ProyectoDatos2/Datos2/Imagenes/PCB/Pines MOSFET 1.jpg

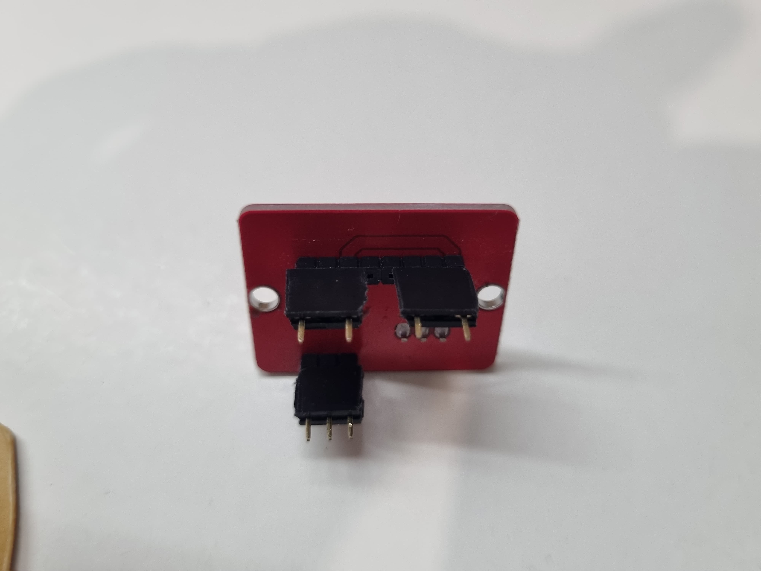
Imagenes/PCB/Pines MOSFET 1.jpg
