ProyectoDatos2/Datos2/Imagenes/PCB/Pines MOSFET 2.jpg

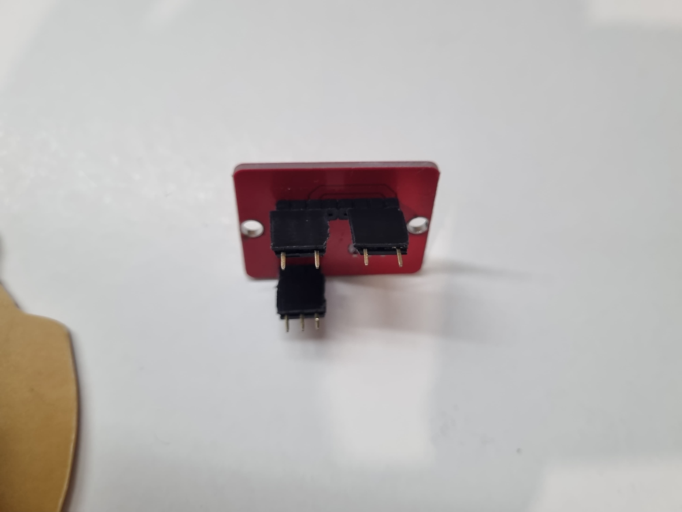
Imagenes/PCB/Pines MOSFET 2.jpg
