ProyectoDatos2/Datos2/Imagenes/PCB/Pines Placa.png

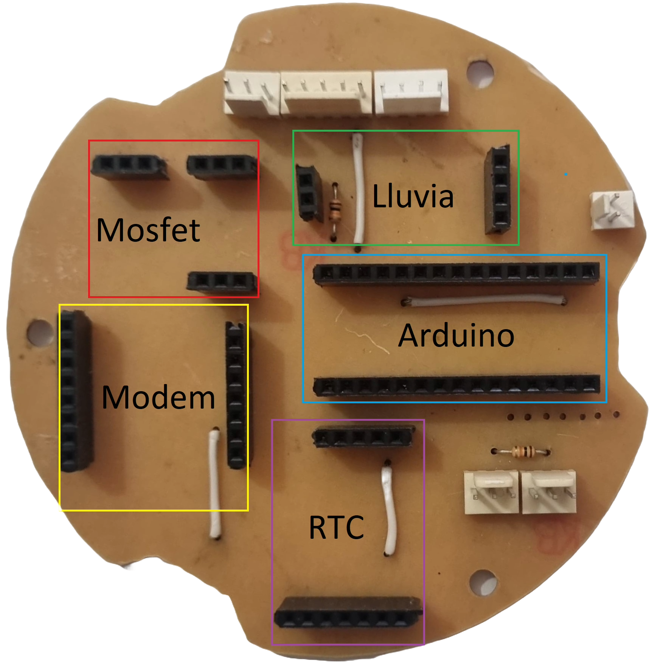
Imagenes/PCB/Pines Placa.png
