ProyectoDatos2/Datos2/Imagenes/PCB/Placa Terminada.png

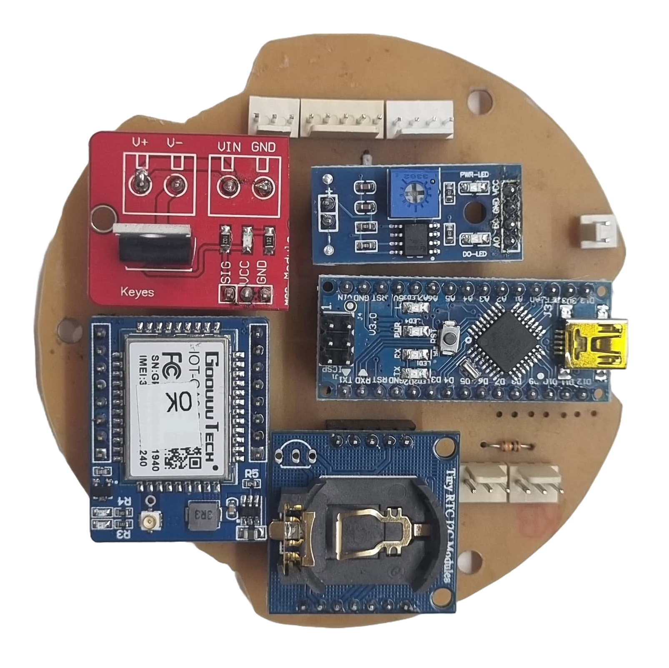
Imagenes/PCB/Placa Terminada.png
