ProyectoDatos2/Datos2/Imagenes/PCB/Posicion Pila RTC.jpg

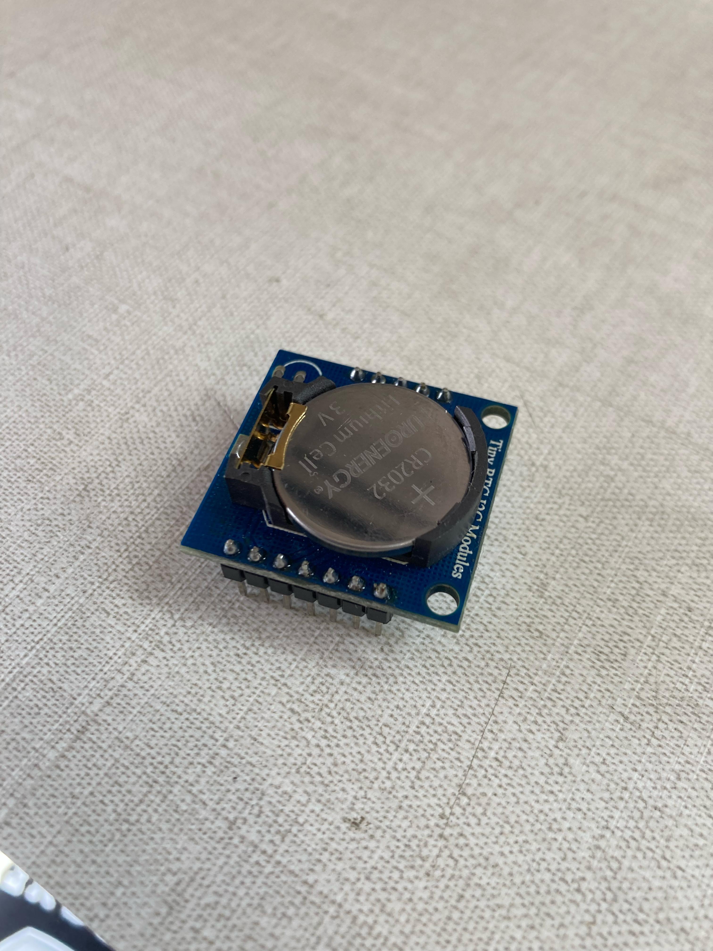
Imagenes/PCB/Posicion Pila RTC.jpg
