ProyectoDatos2/Datos2/Imagenes/PCB/Prensa Cables para Antena.jpg

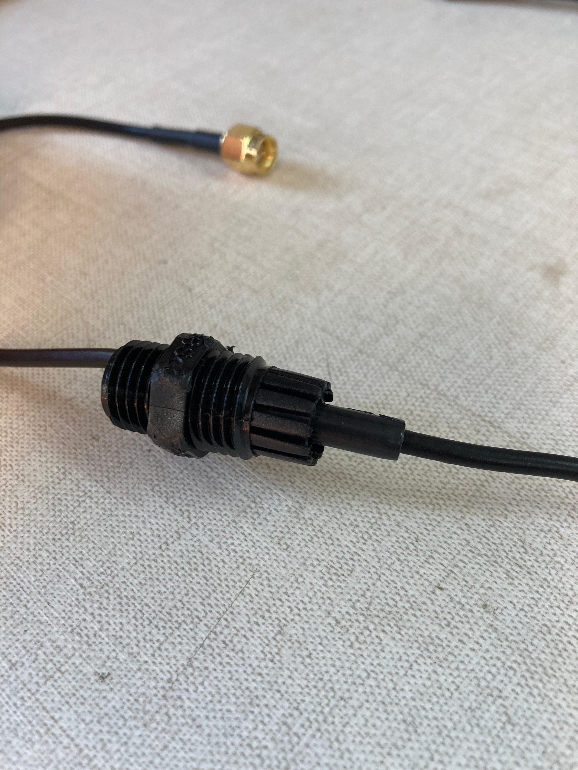
Imagenes/PCB/Prensa Cables para Antena.jpg
