ProyectoDatos2/Datos2/Imagenes/PCB/Componentes Necesarios.jpg

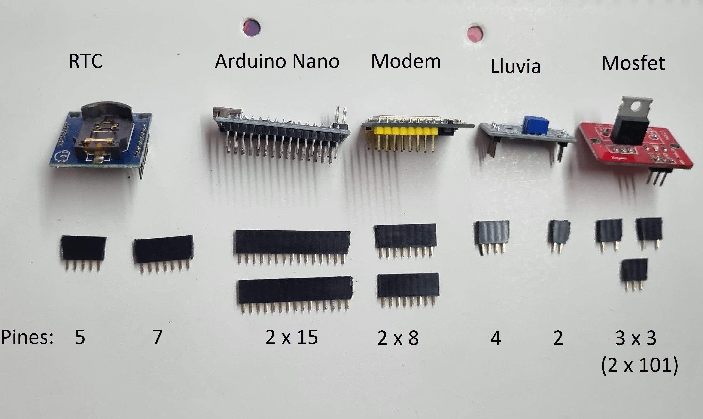
Imagenes/PCB/Componentes Necesarios.jpg
