ProyectoDatos2/Datos2/Impresion 3D STL/Telemetría/Tel_Holder Step Up.STL

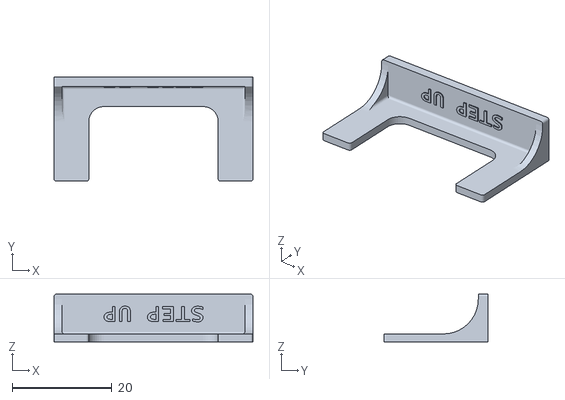
[picture p59: CAD file, 2023-10-26]
Impresion 3D STL/Telemetría/Tel_Holder Step Up.STL
40.0 x 21.0 x 9.60
