ProyectoDatos2/Datos2/Impresion 3D STL/Pluviómetro/Pluv_Estanco A.STL

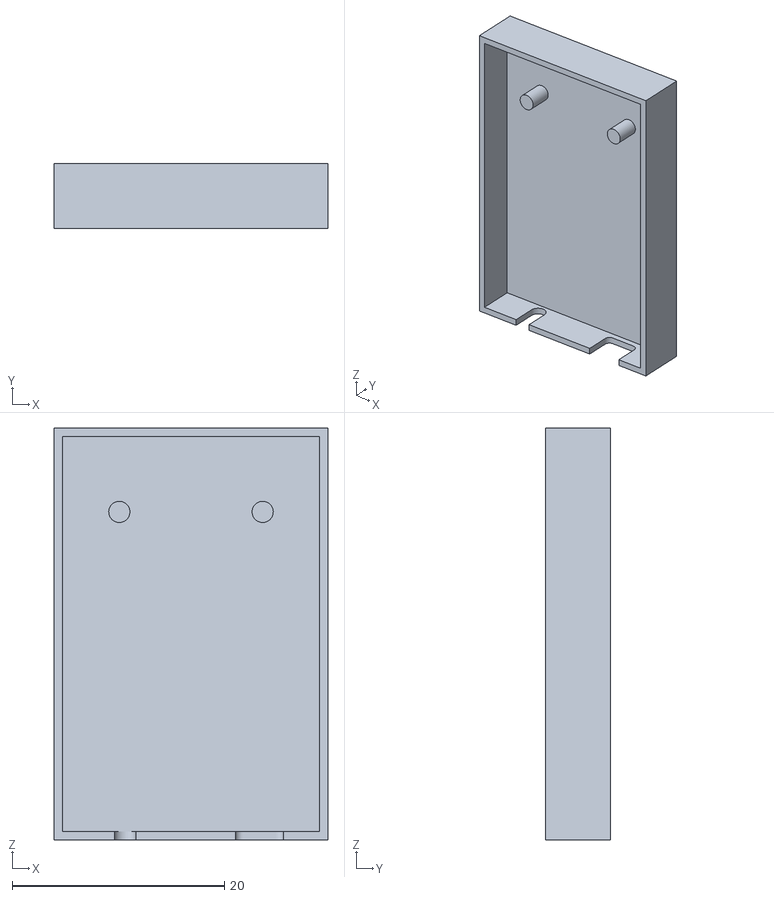
[picture p60: CAD file, 2023-10-26]
Impresion 3D STL/Pluviómetro/Pluv_Estanco A.STL
25.8 x 6.10 x 38.8
