ProyectoDatos2/Datos2/Impresion 3D STL/Telemetría/Tel_Tope.STL

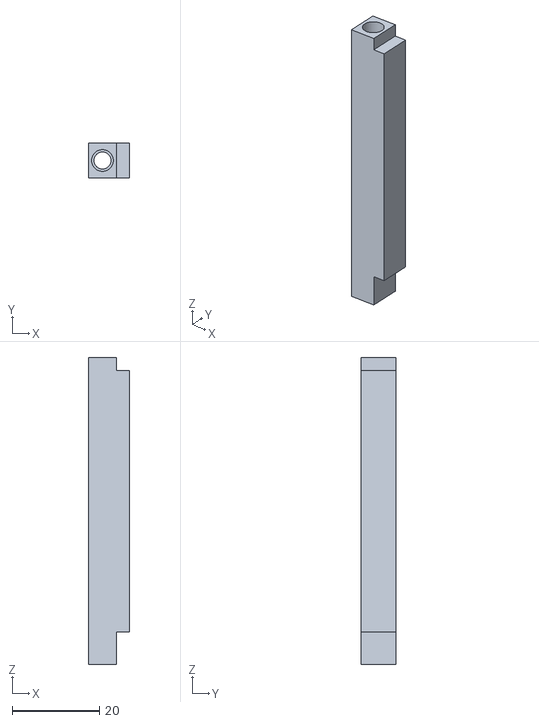
[picture p61: CAD file, 2023-10-26]
Impresion 3D STL/Telemetría/Tel_Tope.STL
9.50 x 8.00 x 70.5
