ProyectoDatos2/Datos2/Impresion 3D STL/Pluviómetro/Pluv_Aro.STL

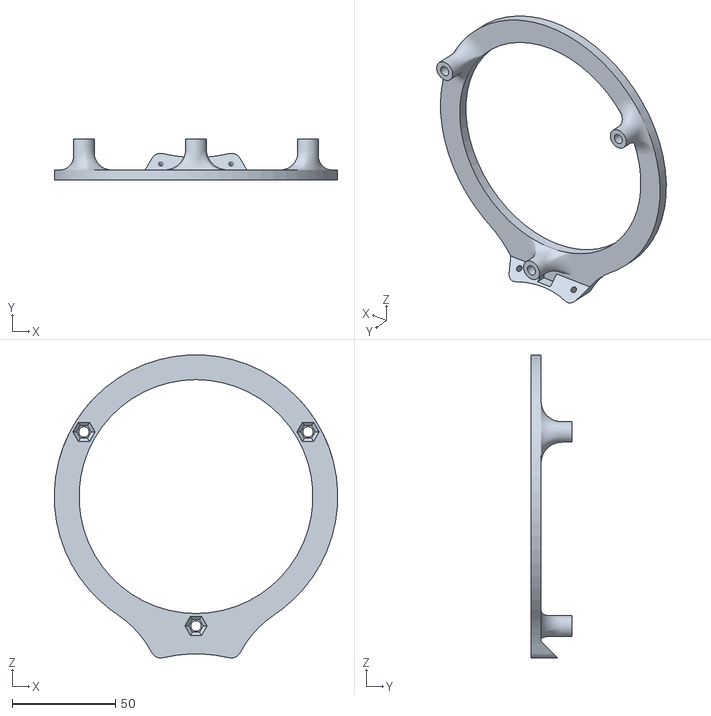
[picture p62: CAD file, 2023-10-26]
Impresion 3D STL/Pluviómetro/Pluv_Aro.STL
136.9 x 20.0 x 146.4
