ProyectoDatos2/Datos2/Impresion 3D STL/Telemetría/Tel_Tapa Inferior.STL

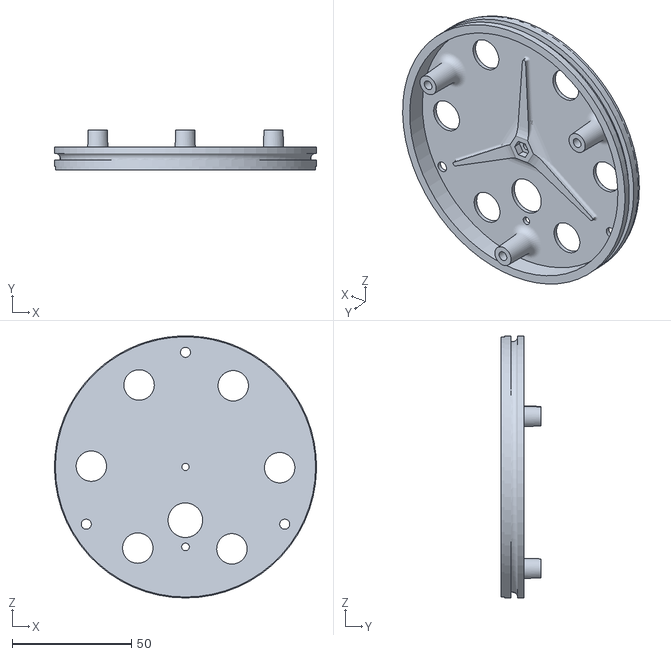
[picture p63: CAD file, 2023-10-26]
Impresion 3D STL/Telemetría/Tel_Tapa Inferior.STL
109.8 x 16.6 x 109.7
