ProyectoDatos2/Datos2/Impresion 3D STL/Pluviómetro/Pluv_Tapa.STL

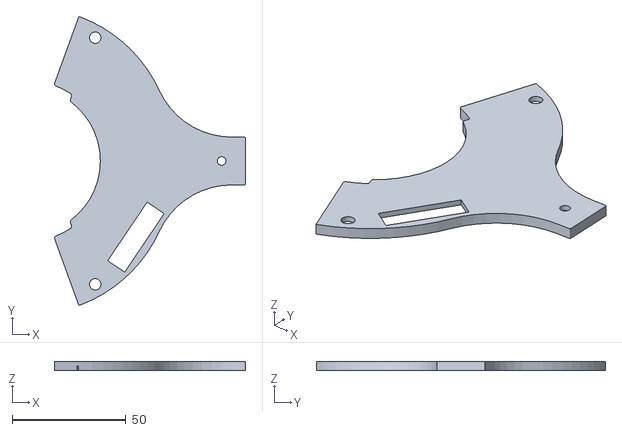
[picture p64: CAD file, 2023-10-26]
Impresion 3D STL/Pluviómetro/Pluv_Tapa.STL
83.8 x 126.9 x 4.00
