ProyectoDatos2/Datos2/Impresion 3D STL/Telemetría/Tel_Pieza T.STL

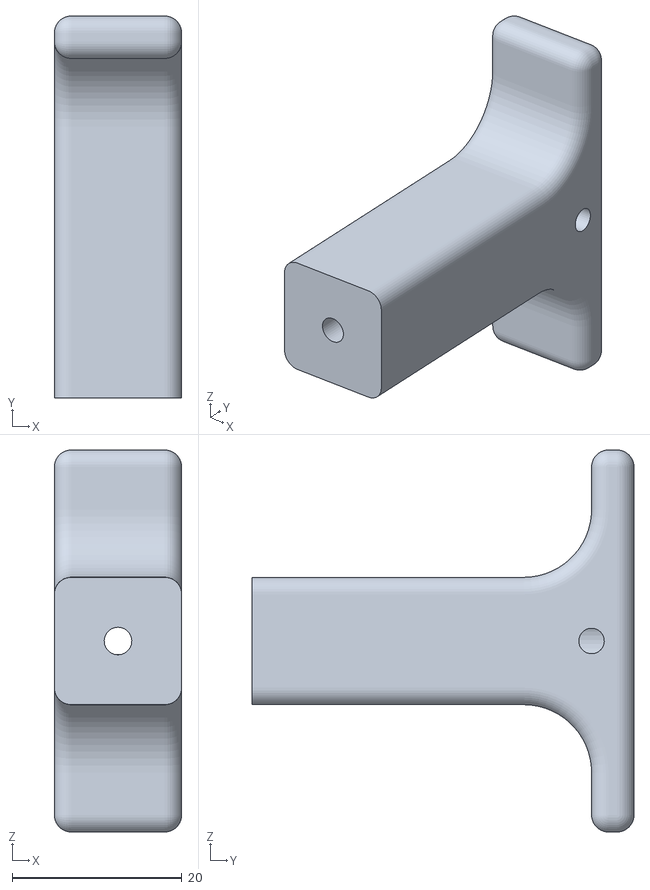
[picture p65: CAD file, 2023-10-26]
Impresion 3D STL/Telemetría/Tel_Pieza T.STL
15.0 x 45.0 x 45.0
