ProyectoDatos2/Datos2/Impresion 3D STL/Telemetría/Tel_Separador.STL

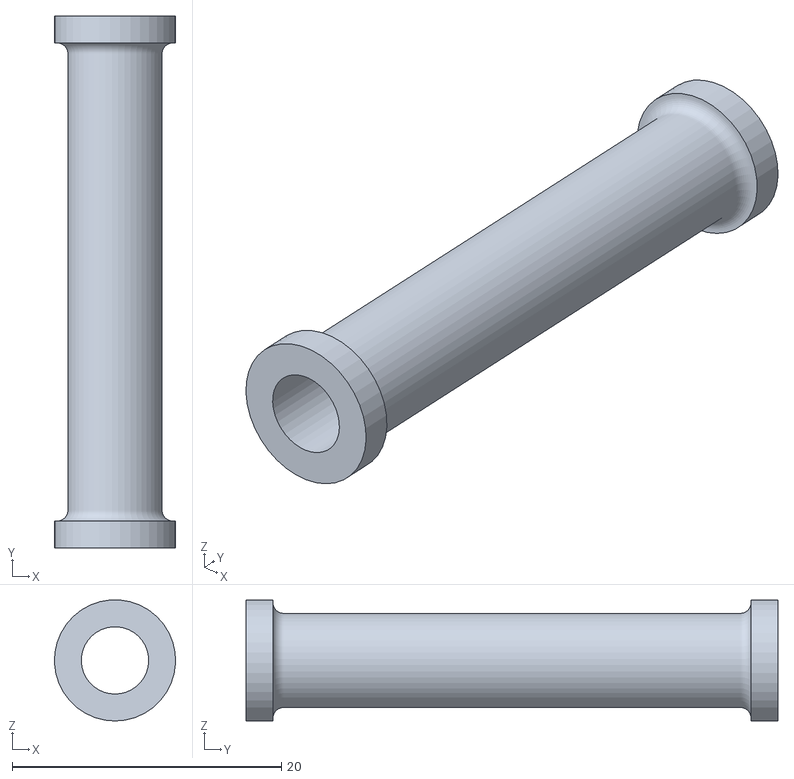
[picture p66: CAD file, 2023-10-26]
Impresion 3D STL/Telemetría/Tel_Separador.STL
8.99 x 39.5 x 8.98
