ProyectoDatos2/Datos2/Imagenes/Ensamble/Conjunto Pluviómetro/Arandelas Localizador.jpg

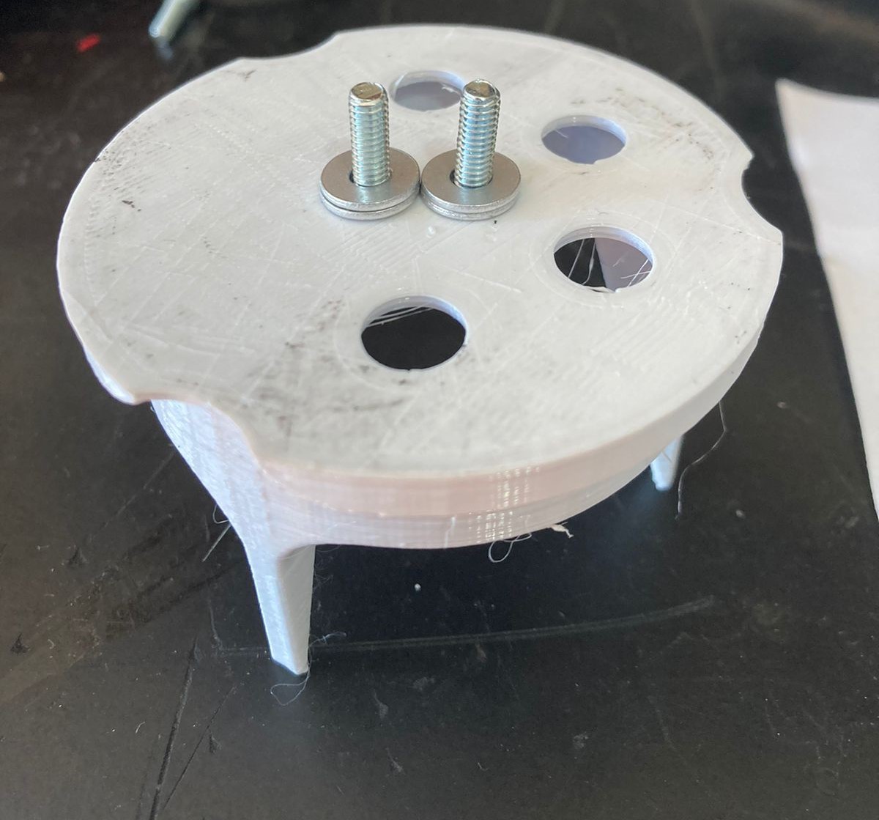
Imagenes/Ensamble/Conjunto Pluviómetro/Arandelas Localizador.jpg
