ProyectoDatos2/Datos2/Imagenes/Ensamble/Conjunto Pluviómetro/Colocacion Driver Celda de Carga 2.jpg

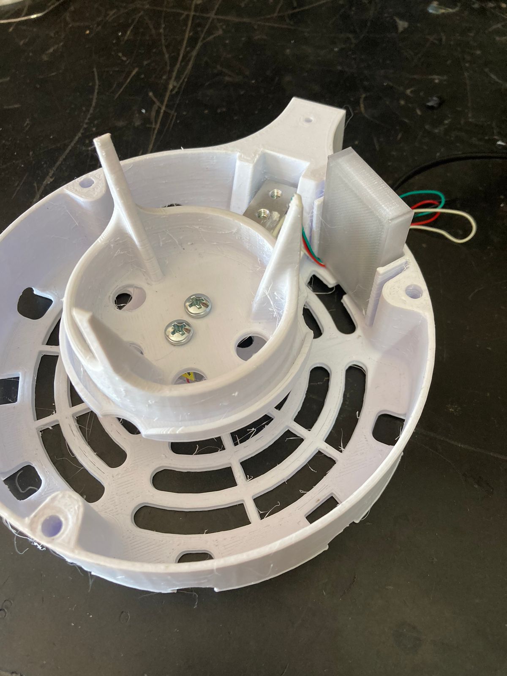
Imagenes/Ensamble/Conjunto Pluviómetro/Colocacion Driver Celda de Carga 2.jpg
