ProyectoDatos2/Datos2/Imagenes/Ensamble/Conjunto Pluviómetro/Colocación Mensula.jpg

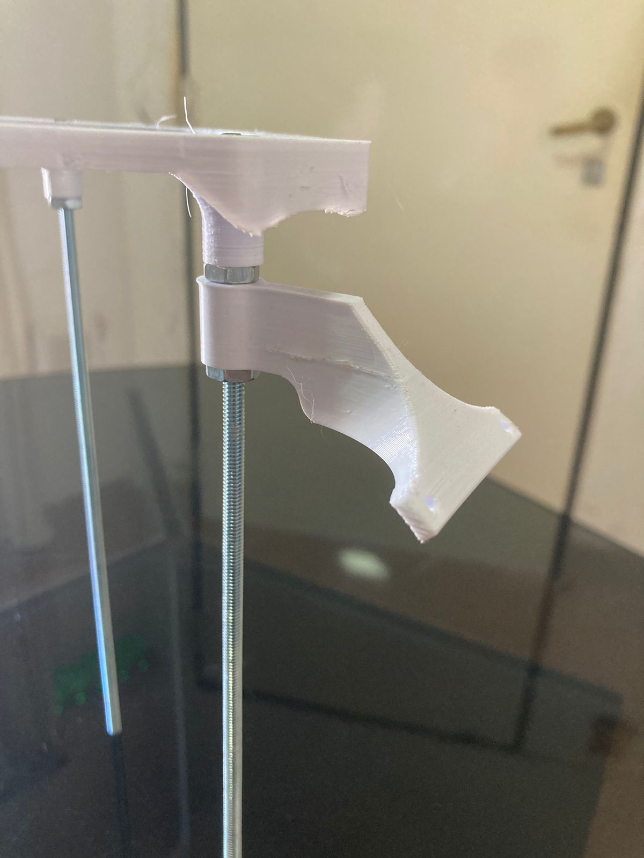
Imagenes/Ensamble/Conjunto Pluviómetro/Colocación Mensula.jpg
