ProyectoDatos2/Datos2/Imagenes/Ensamble/Conjunto Pluviómetro/Colocación Tapa.jpg

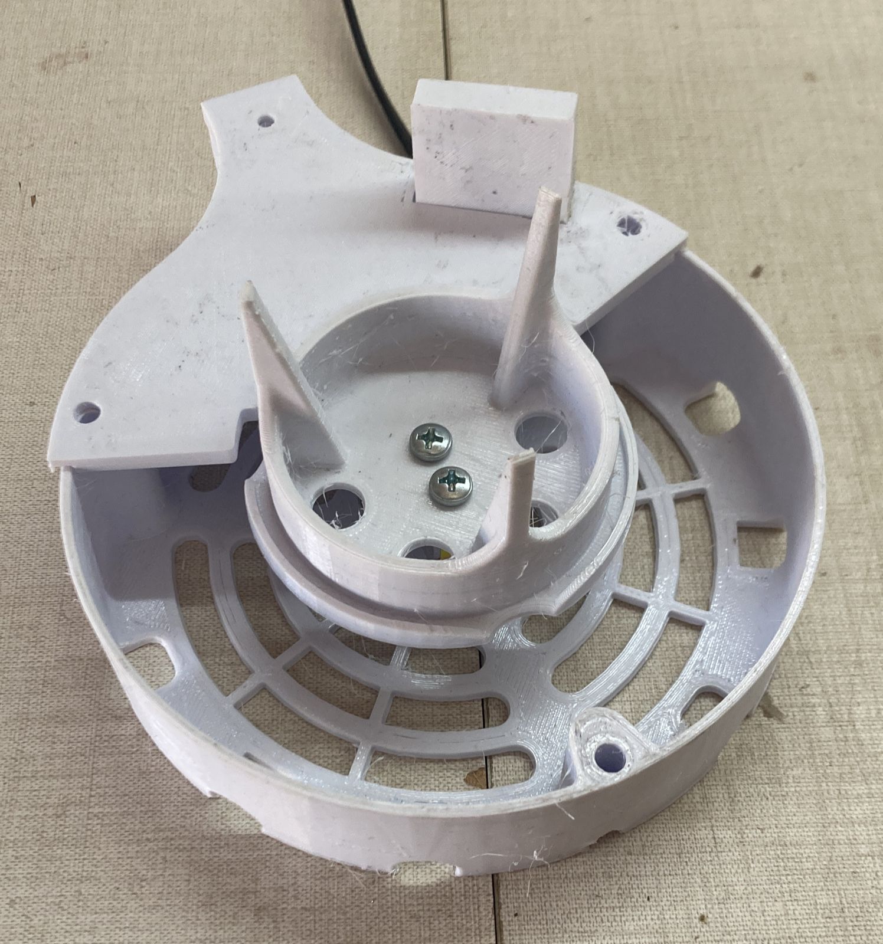
Imagenes/Ensamble/Conjunto Pluviómetro/Colocación Tapa.jpg
