ProyectoDatos2/Datos2/Imagenes/Ensamble/Conjunto Pluviómetro/Conexión Celda de Carga.png

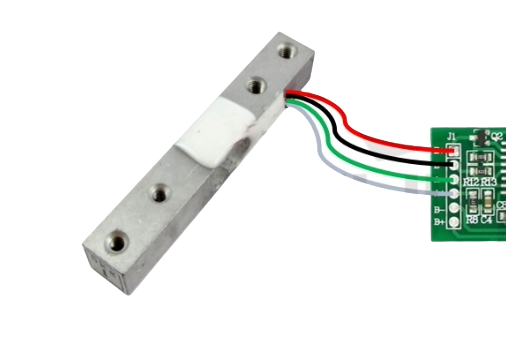
Imagenes/Ensamble/Conjunto Pluviómetro/Conexión Celda de Carga.png
