ProyectoDatos2/Datos2/Imagenes/Ensamble/Conjunto Pluviómetro/Nivel 1.jpg

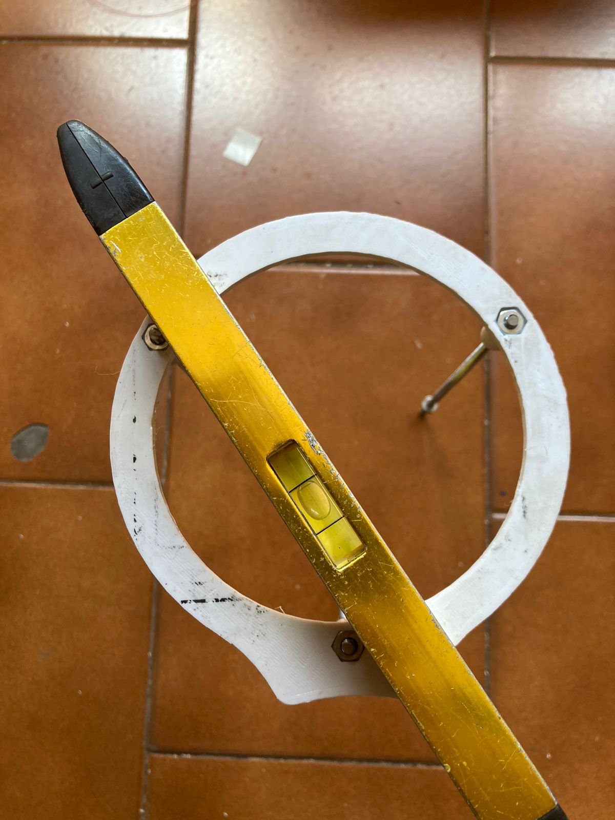
Imagenes/Ensamble/Conjunto Pluviómetro/Nivel 1.jpg
