ProyectoDatos2/Datos2/Imagenes/Ensamble/Conjunto Pluviómetro/Nivel 2.jpg

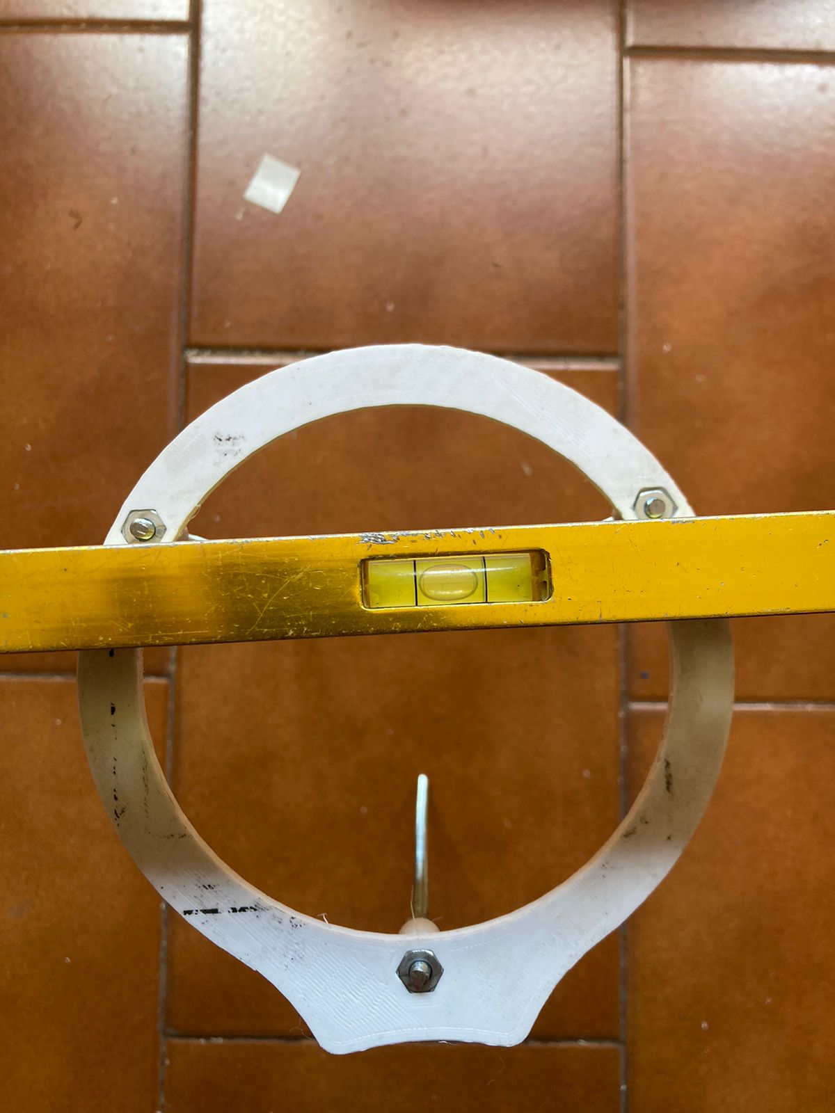
Imagenes/Ensamble/Conjunto Pluviómetro/Nivel 2.jpg
