ProyectoDatos2/Datos2/Imagenes/Ensamble/Conjunto Pluviómetro/Nivel 3.jpg

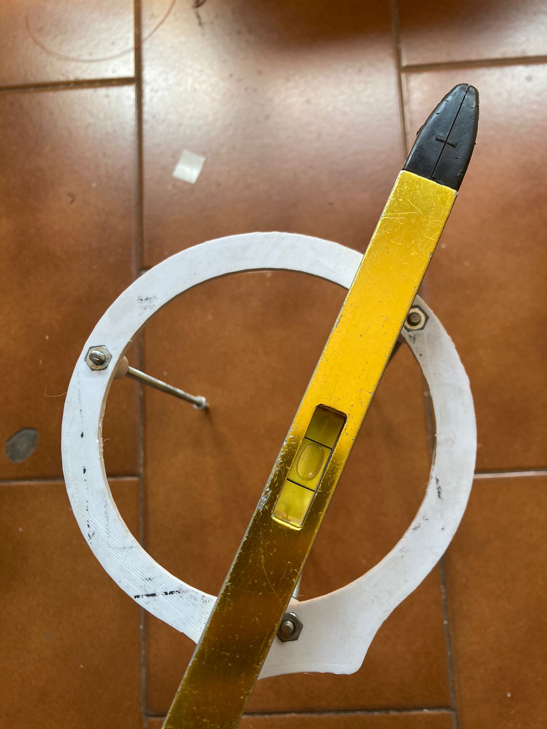
Imagenes/Ensamble/Conjunto Pluviómetro/Nivel 3.jpg
