ProyectoDatos2/Datos2/Imagenes/Ensamble/Conjunto Pluviómetro/Orientacion Localizador.jpg

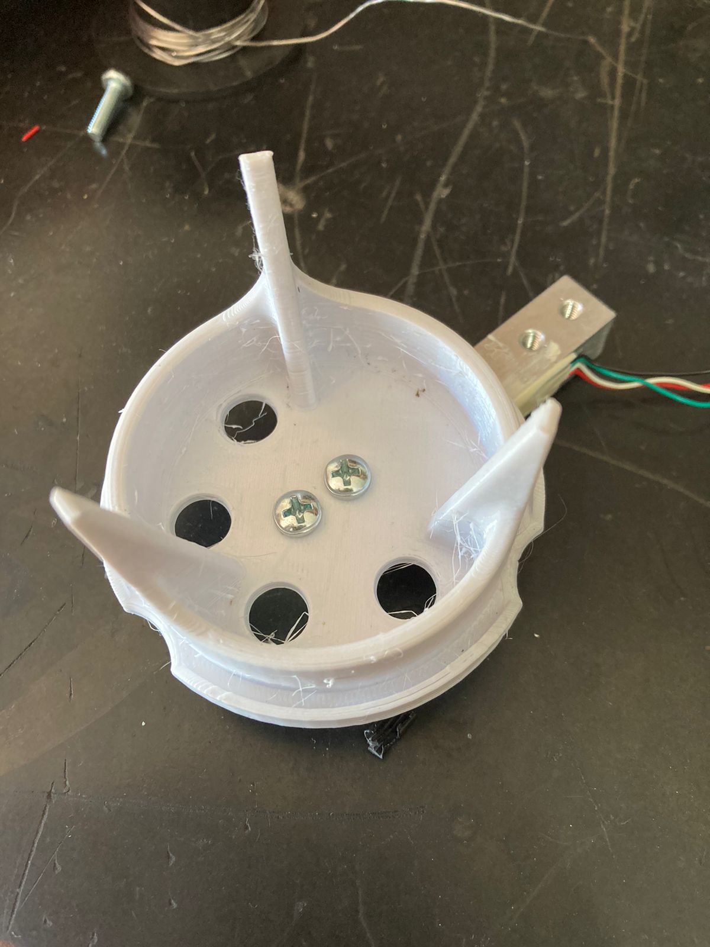
Imagenes/Ensamble/Conjunto Pluviómetro/Orientacion Localizador.jpg
