ProyectoDatos2/Datos2/Imagenes/Ensamble/Conjunto Pluviómetro/Orientación Celda de Carga.jpg

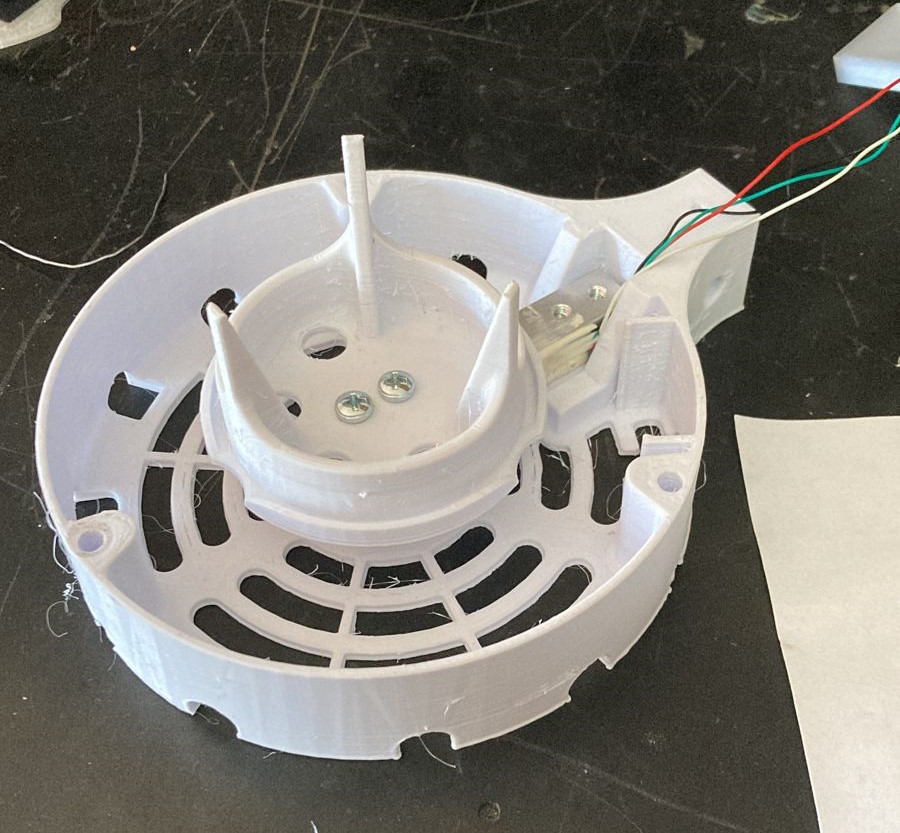
Imagenes/Ensamble/Conjunto Pluviómetro/Orientación Celda de Carga.jpg
