ProyectoDatos2/Datos2/Imagenes/Ensamble/Conjunto Pluviómetro/Pintado y Colocacion Sensor Raindrop.png

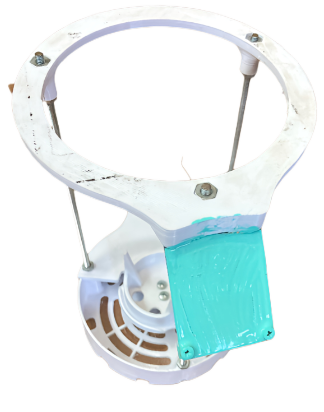
Imagenes/Ensamble/Conjunto Pluviómetro/Pintado y Colocacion Sensor Raindrop.png
