ProyectoDatos2/Datos2/Imagenes/Ensamble/Conjunto Pluviómetro/Roscas por Abajo.jpg

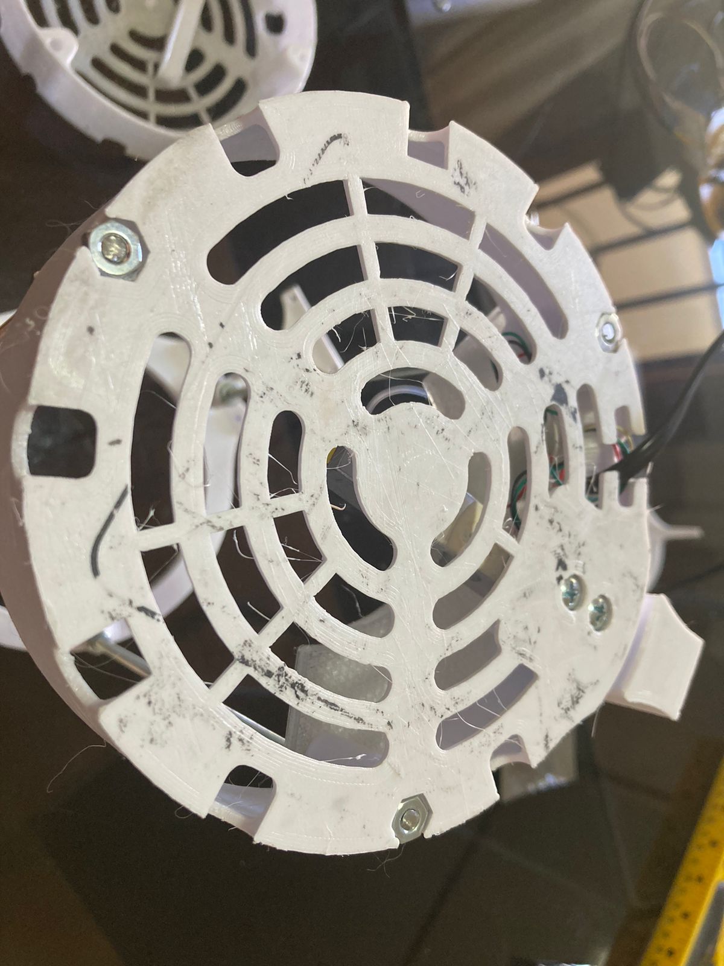
Imagenes/Ensamble/Conjunto Pluviómetro/Roscas por Abajo.jpg
