ProyectoDatos2/Datos2/Imagenes/Ensamble/Conjunto Pluviómetro/Terminado.png

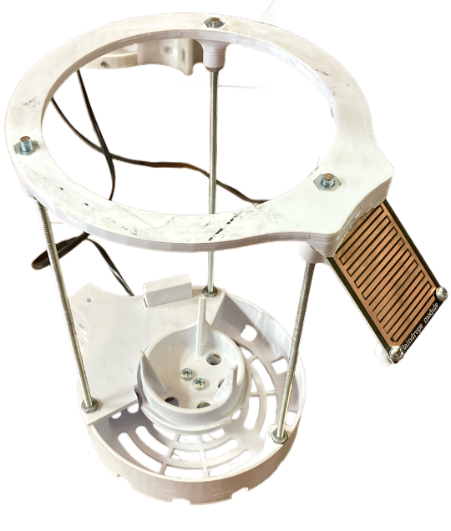
Imagenes/Ensamble/Conjunto Pluviómetro/Terminado.png
