ProyectoDatos2/Datos2/Imagenes/Ensamble/Conjunto UV/Colocación Sensor UV.png

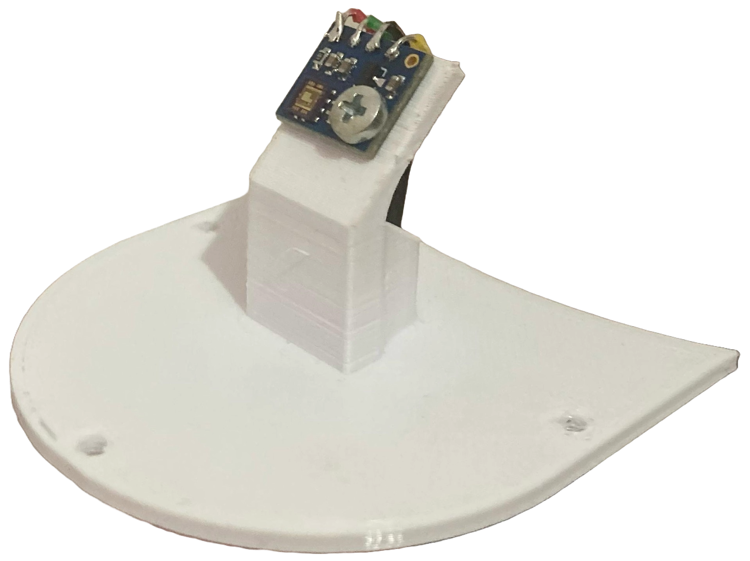
Imagenes/Ensamble/Conjunto UV/Colocación Sensor UV.png
