ProyectoDatos2/Datos2/Imagenes/Ensamble/Conjunto UV/Lente Sensor UV.jpg

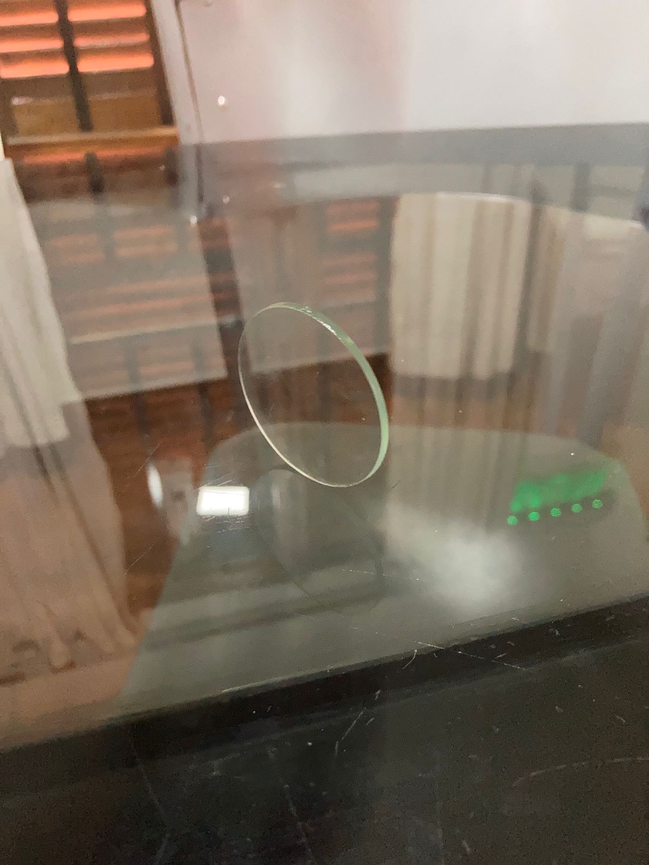
Imagenes/Ensamble/Conjunto UV/Lente Sensor UV.jpg
