ProyectoDatos2/Datos2/Imagenes/Ensamble/Conjunto UV/Posicion Sensor UV.jpg

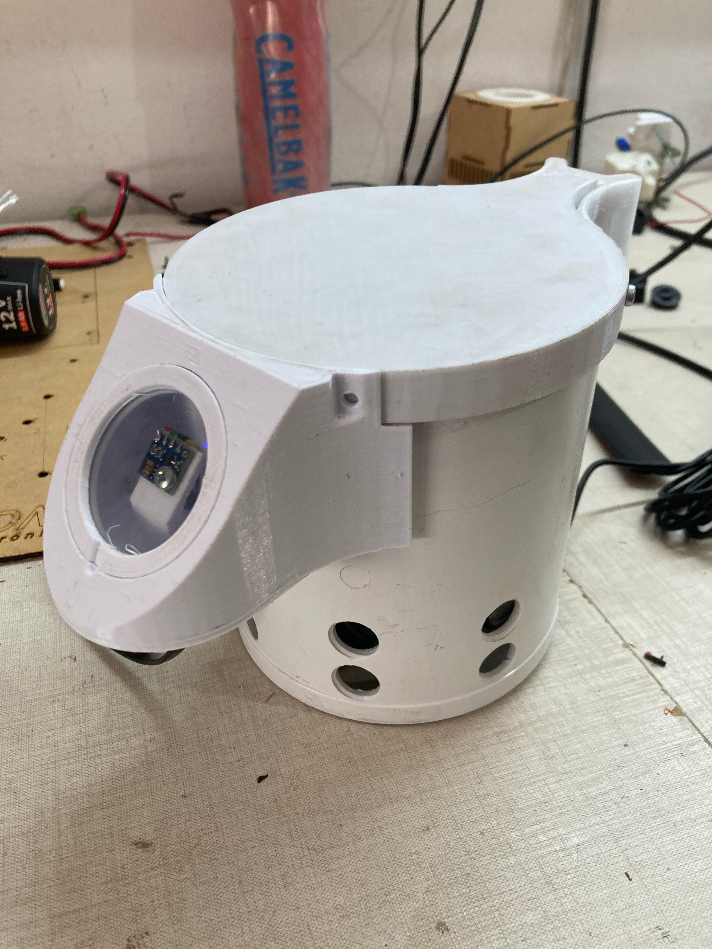
Imagenes/Ensamble/Conjunto UV/Posicion Sensor UV.jpg
