ProyectoDatos2/Datos2/Imagenes/Ensamble/Sistema de Autonomía/Cable Negativo a Step Up.jpg

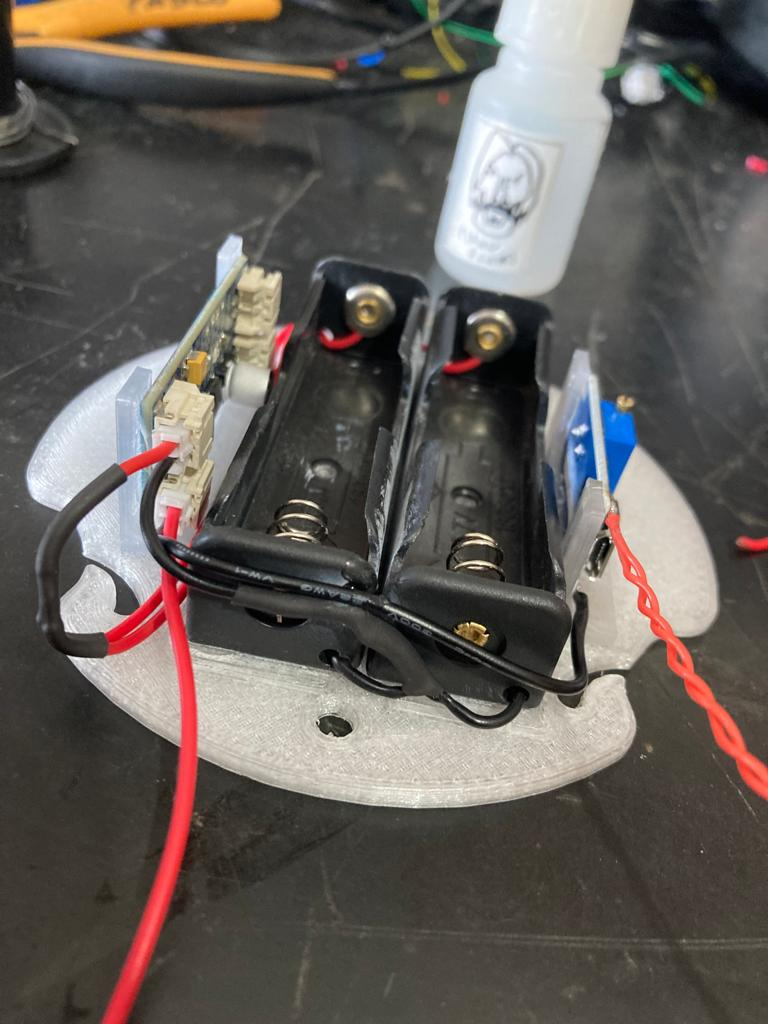
Imagenes/Ensamble/Sistema de Autonomía/Cable Negativo a Step Up.jpg
