ProyectoDatos2/Datos2/Imagenes/Ensamble/Sistema de Autonomía/Cable Positivo por Abajo.jpg

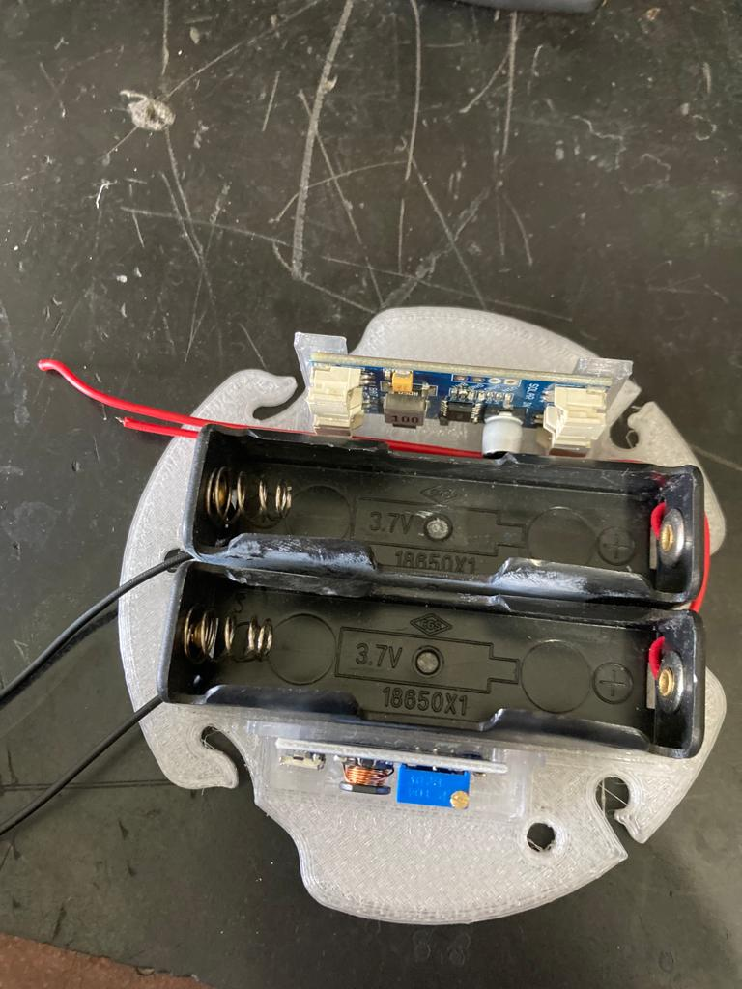
Imagenes/Ensamble/Sistema de Autonomía/Cable Positivo por Abajo.jpg
