ProyectoDatos2/Datos2/Imagenes/Ensamble/Sistema de Autonomía/Conexionado Cargador Solar.jpg

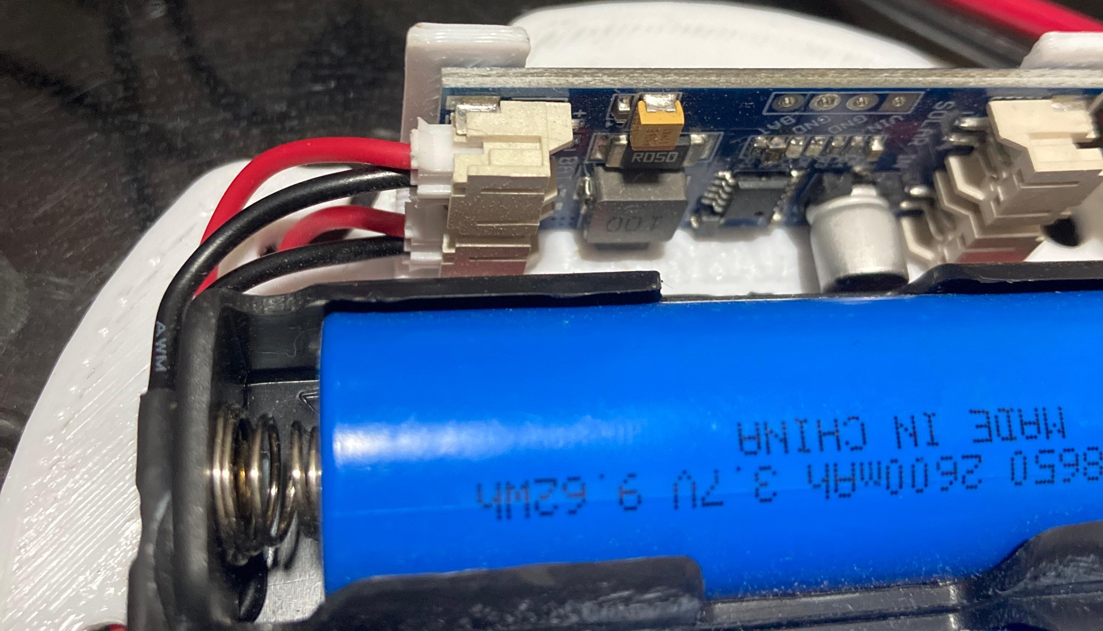
Imagenes/Ensamble/Sistema de Autonomía/Conexionado Cargador Solar.jpg
