ProyectoDatos2/Datos2/Imagenes/Ensamble/Sistema de Autonomía/Conexionado Panel Solar.jpg

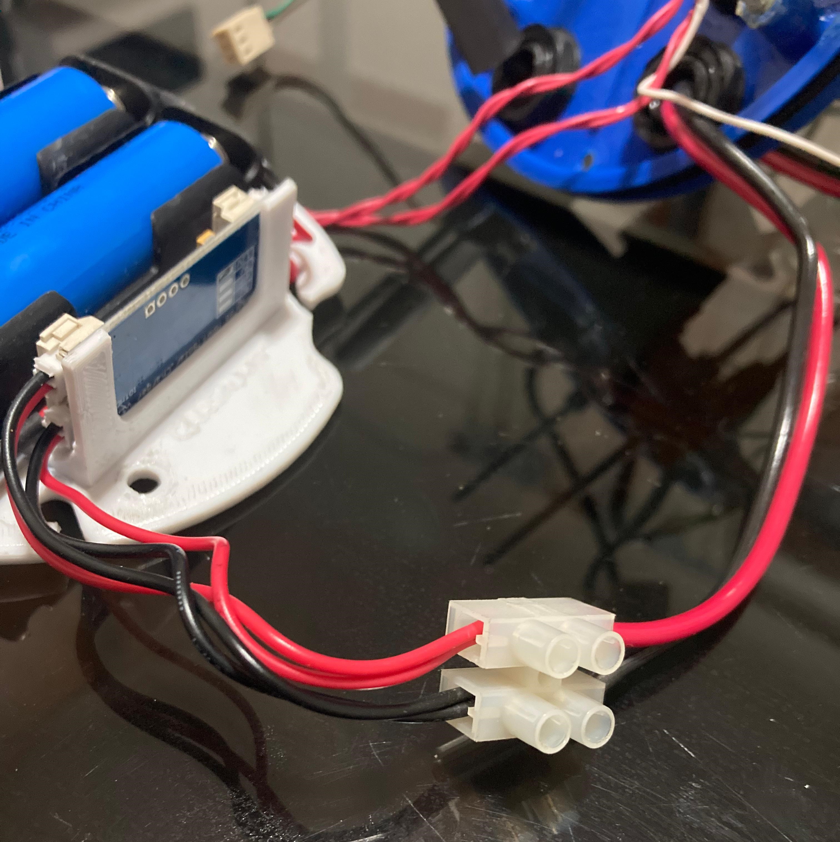
Imagenes/Ensamble/Sistema de Autonomía/Conexionado Panel Solar.jpg
