ProyectoDatos2/Datos2/Imagenes/Ensamble/Sistema de Autonomía/Conexionado Step Up.jpg

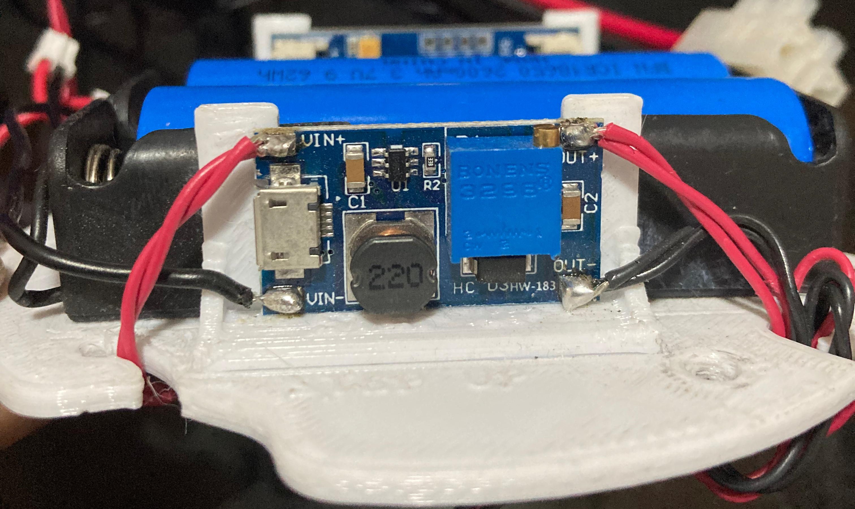
Imagenes/Ensamble/Sistema de Autonomía/Conexionado Step Up.jpg
