ProyectoDatos2/Datos2/Imagenes/Ensamble/Sistema de Autonomía/Empalme Positivos.jpg

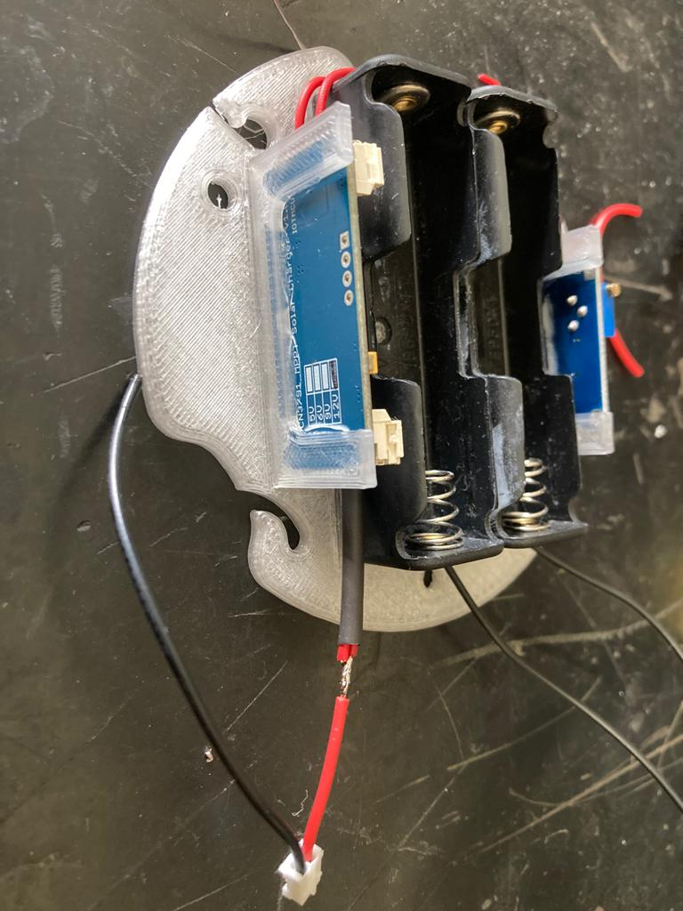
Imagenes/Ensamble/Sistema de Autonomía/Empalme Positivos.jpg
