ProyectoDatos2/Datos2/Imagenes/Ensamble/Sistema General/Colocación Pieza en T.jpg

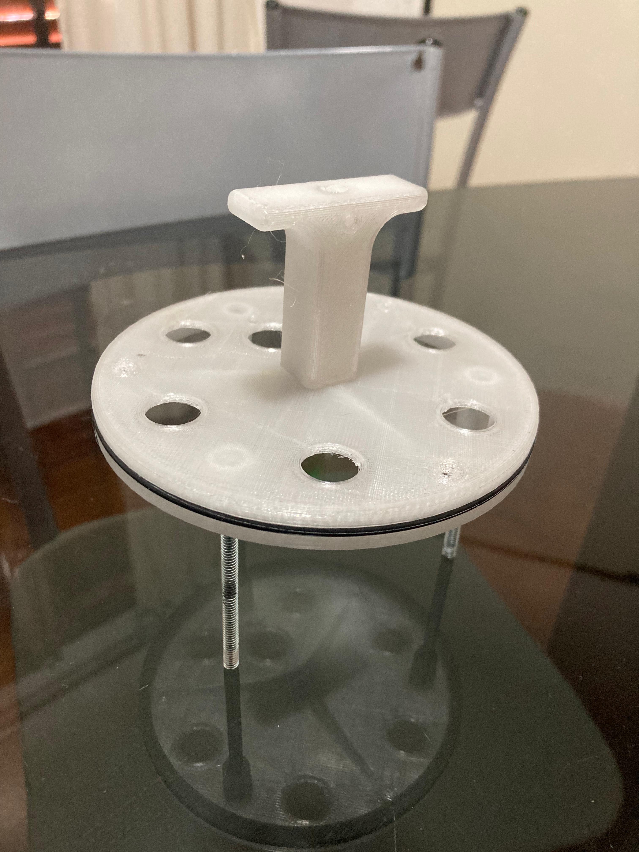
Imagenes/Ensamble/Sistema General/Colocación Pieza en T.jpg
