ProyectoDatos2/Datos2/Imagenes/Ensamble/Sistema General/Colocación Sensor AHT.jpg

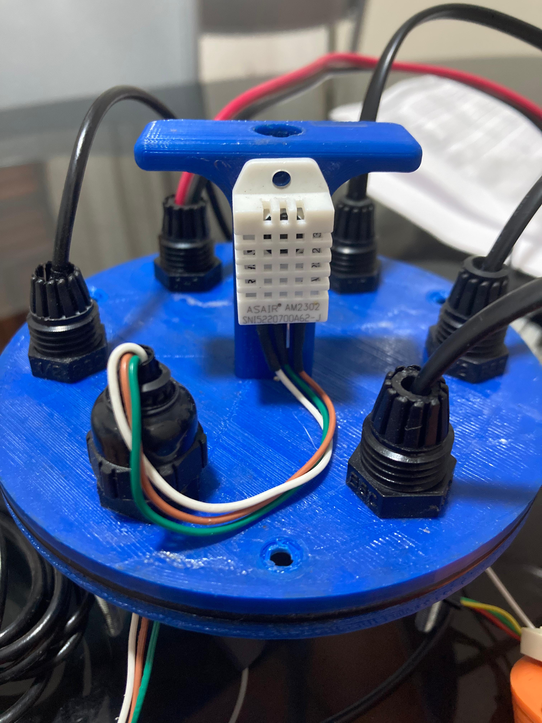
Imagenes/Ensamble/Sistema General/Colocación Sensor AHT.jpg
