ProyectoDatos2/Datos2/Imagenes/Ensamble/Sistema General/O'Ring Colocación.jpg

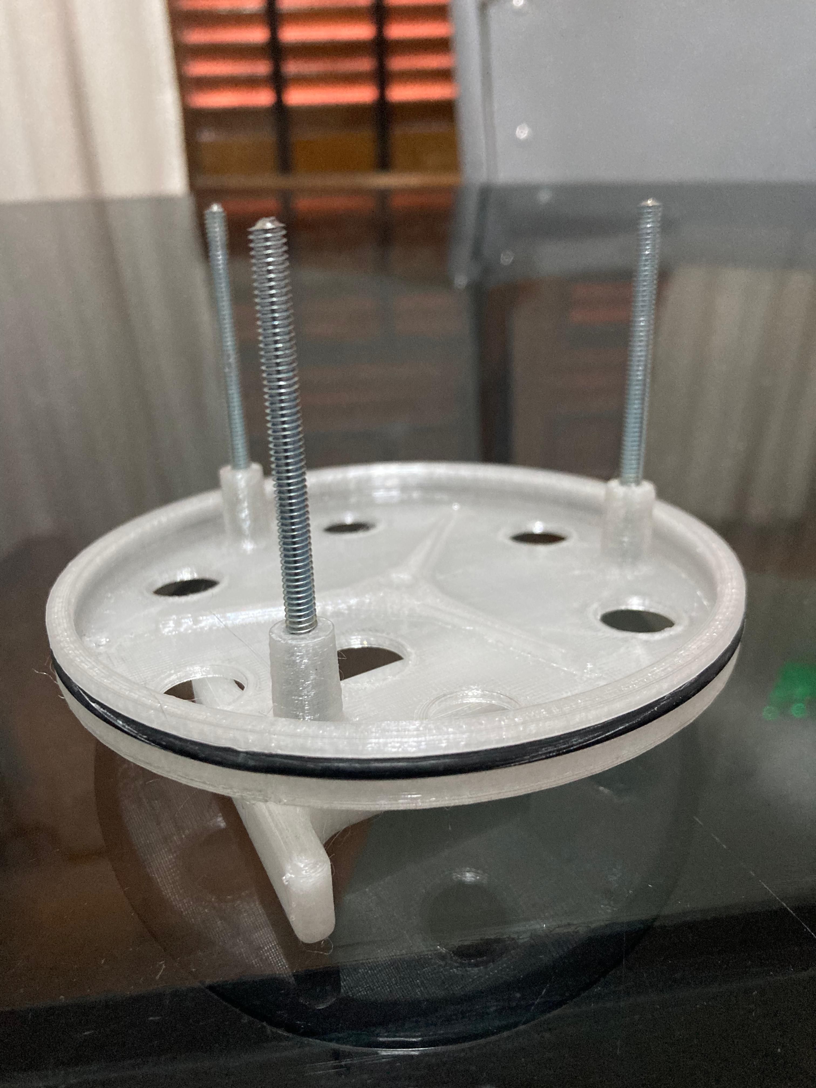
Imagenes/Ensamble/Sistema General/O'Ring Colocación.jpg
