ProyectoDatos2/Datos2/Imagenes/Ensamble/Sistema General/Placa Posicionada.jpg

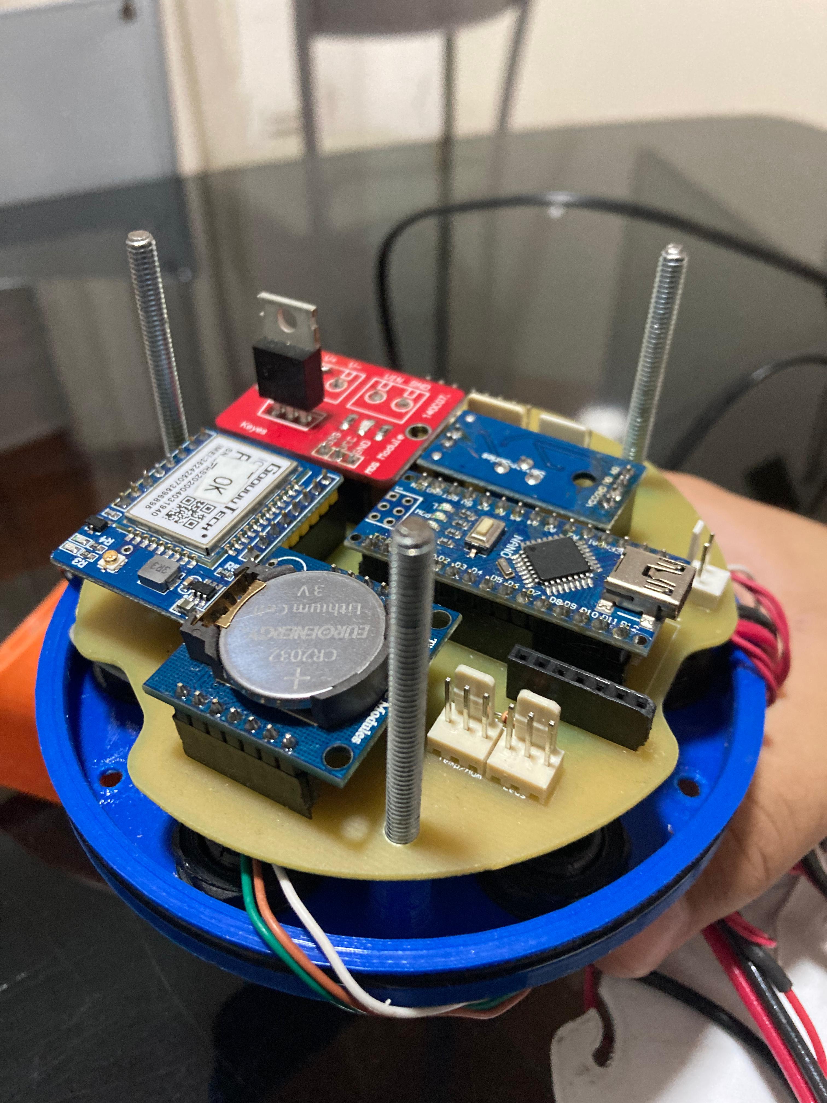
Imagenes/Ensamble/Sistema General/Placa Posicionada.jpg
