ProyectoDatos2/Datos2/Imagenes/Ensamble/Sistema General/Preparado AHT.jpg

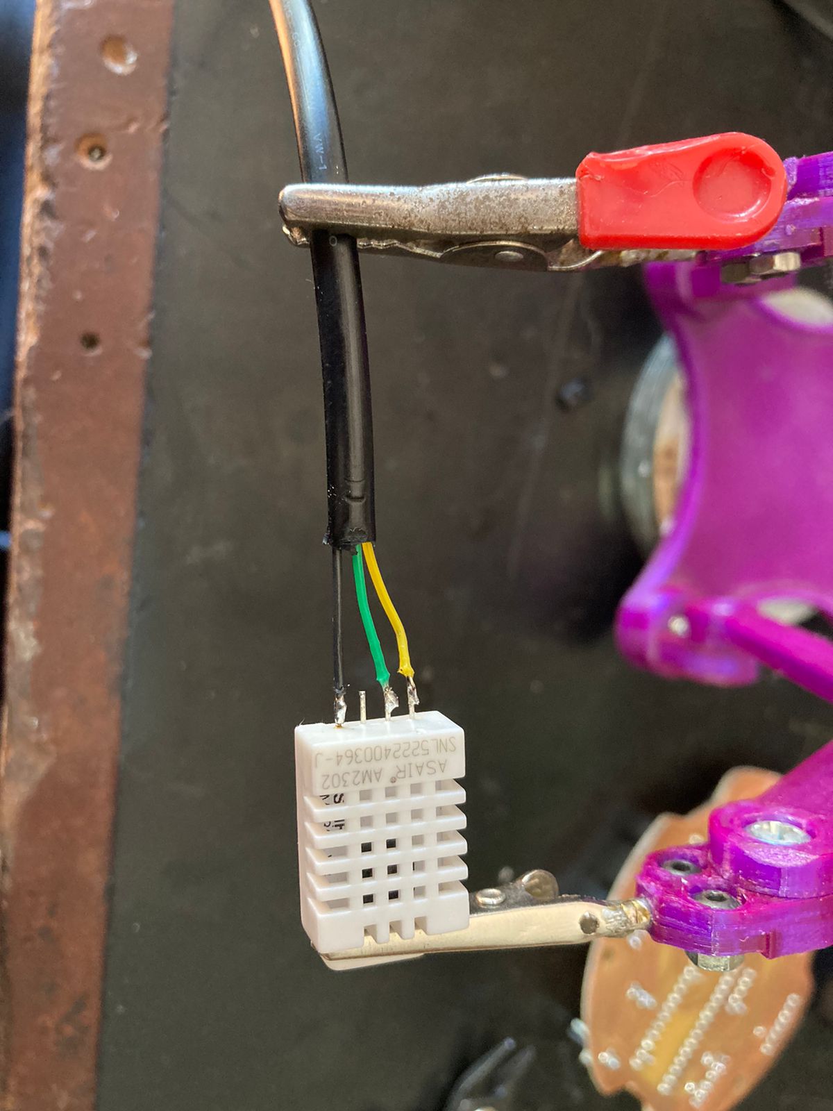
Imagenes/Ensamble/Sistema General/Preparado AHT.jpg
