ProyectoDatos2/Datos2/Imagenes/Ensamble/Sistema General/Tapa con O'Ring.jpg

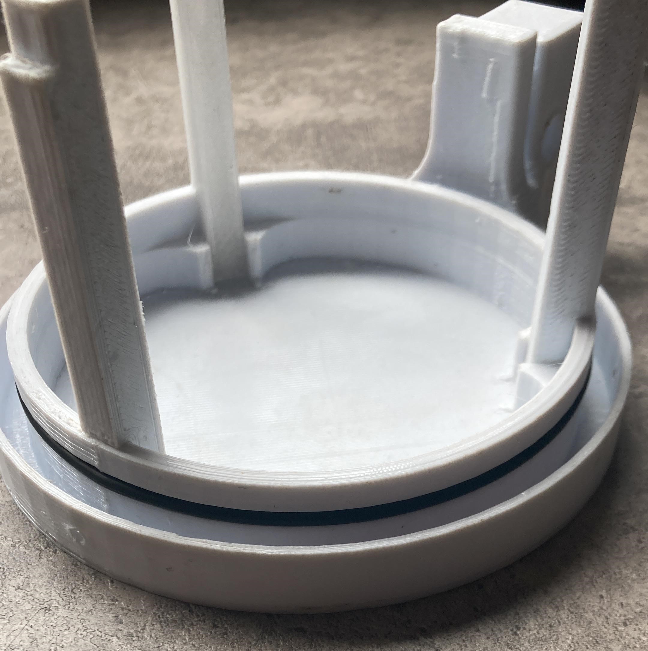
Imagenes/Ensamble/Sistema General/Tapa con O'Ring.jpg
