ProyectoDatos2/Datos2/Imagenes/Ensamble/Sistema General/Tubo Union entre 2 con Tapa.jpg

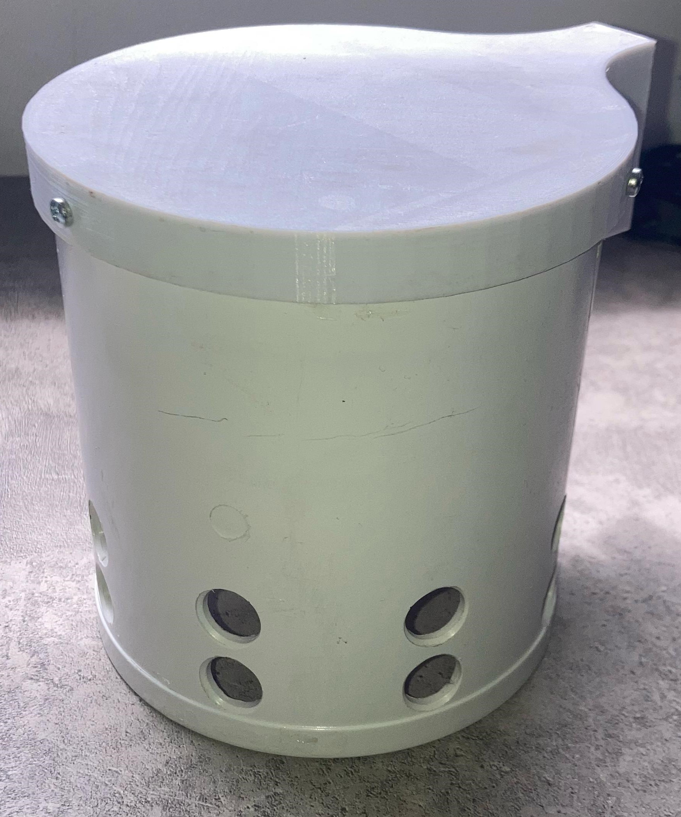
Imagenes/Ensamble/Sistema General/Tubo Union entre 2 con Tapa.jpg
