ProyectoDatos2/Datos2/Imagenes/Ensamble/Sistema General/Tubo Union entre 2.jpg

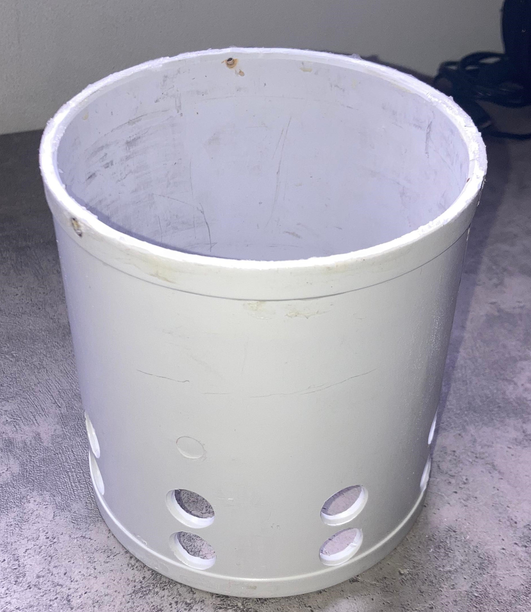
Imagenes/Ensamble/Sistema General/Tubo Union entre 2.jpg
